rileymcdowell/paneled/instructions/30_panel_assembly/images/route_cavity_with_switch.jpg

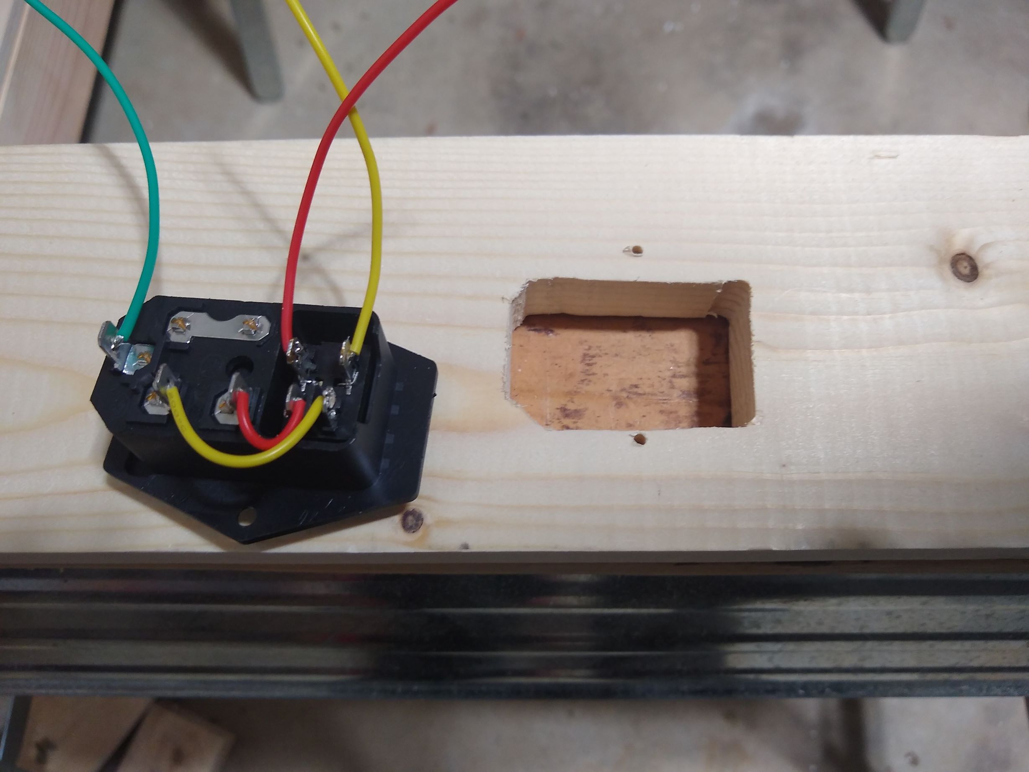
instructions/30_panel_assembly/images/route_cavity_with_switch.jpg
