rileymcdowell/paneled/instructions/30_panel_assembly/images/routing_hole_with_dremel.jpg

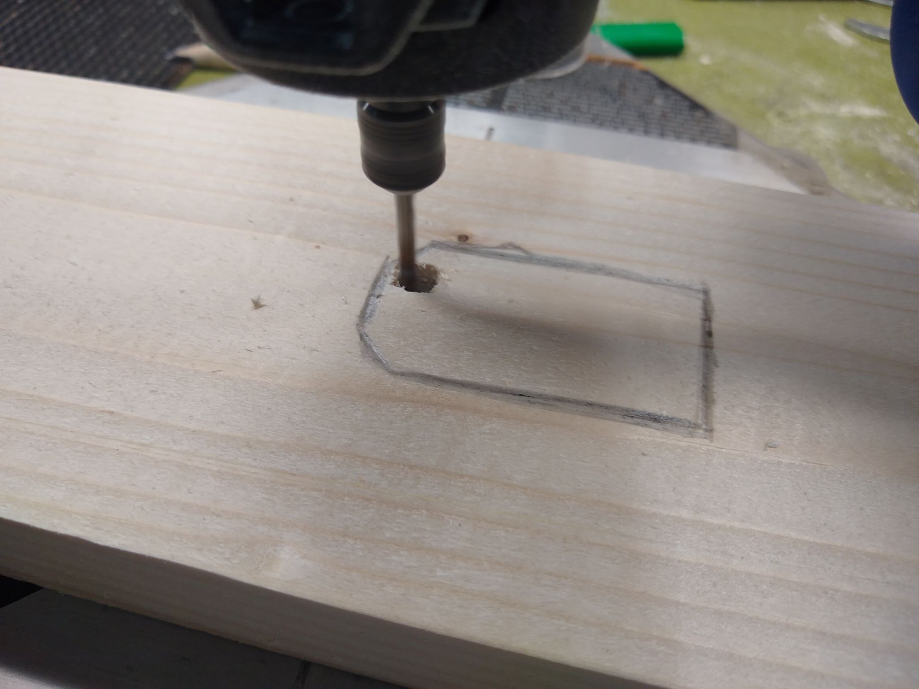
instructions/30_panel_assembly/images/routing_hole_with_dremel.jpg
